morganp/openscad-festool-thincut/makerworld/cover_4x3.jpeg

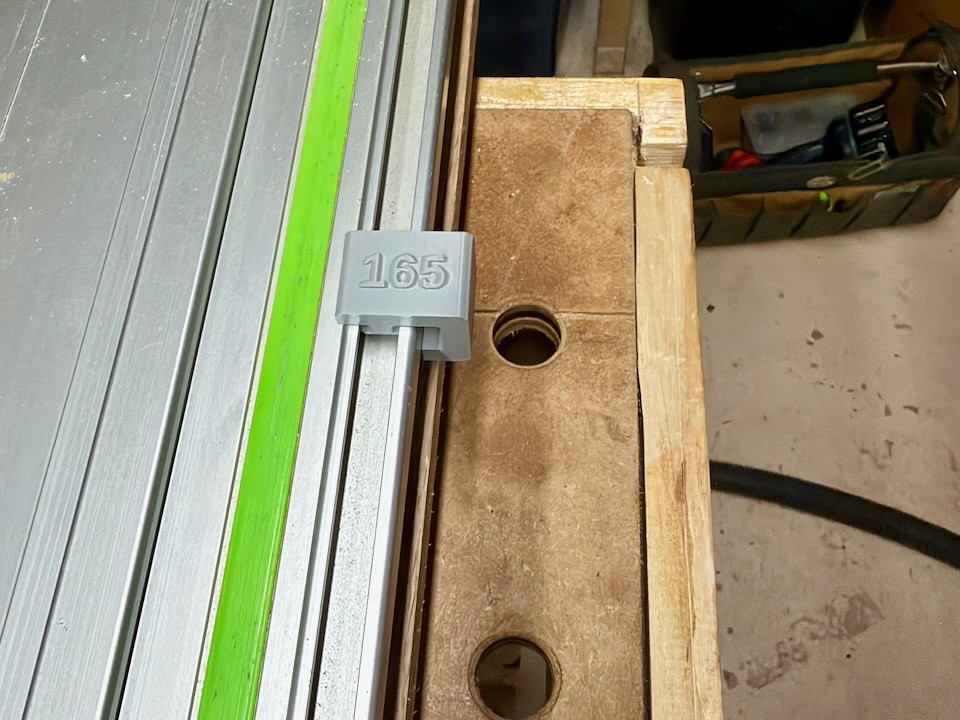
makerworld/cover_4x3.jpeg
