morganp/openscad-festool-thincut/makerworld/photo_2932.jpeg

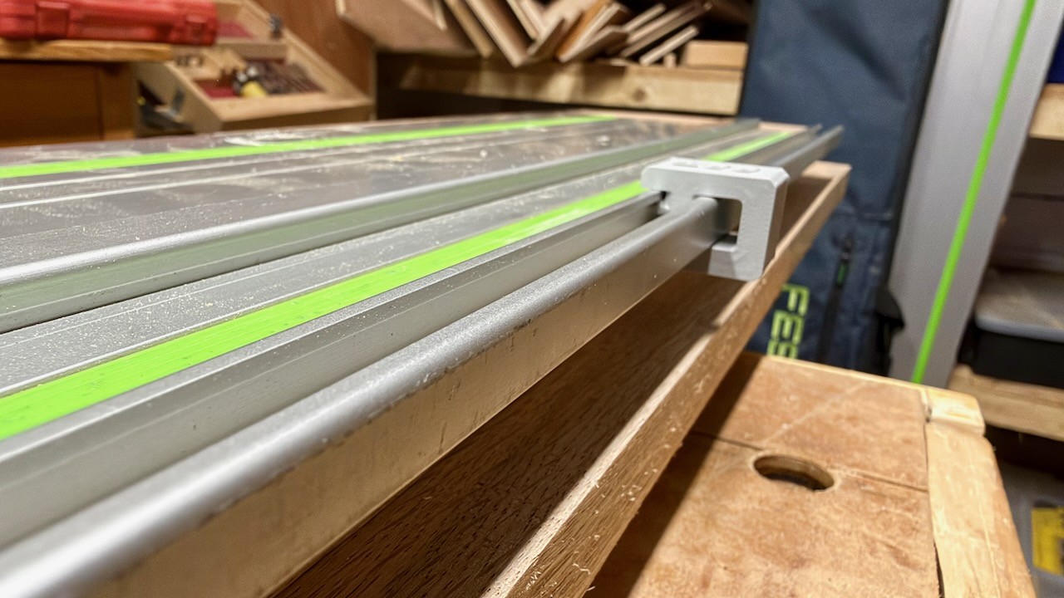
makerworld/photo_2932.jpeg
