morganp/openscad-festool-thincut/makerworld/photo_2934.jpeg

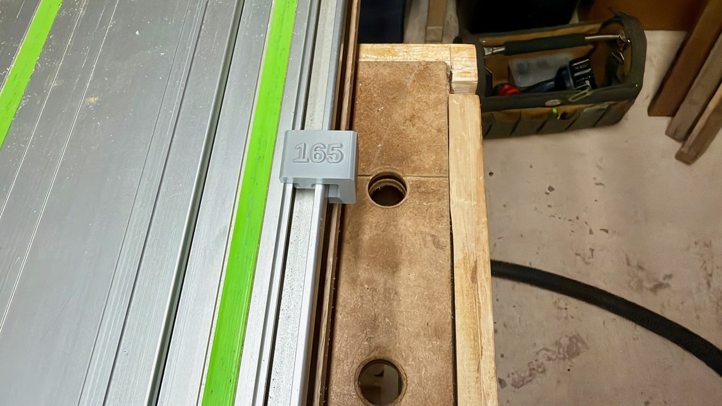
makerworld/photo_2934.jpeg
