morganp/openscad-festool-thincut/makerworld/photo_2935.jpeg

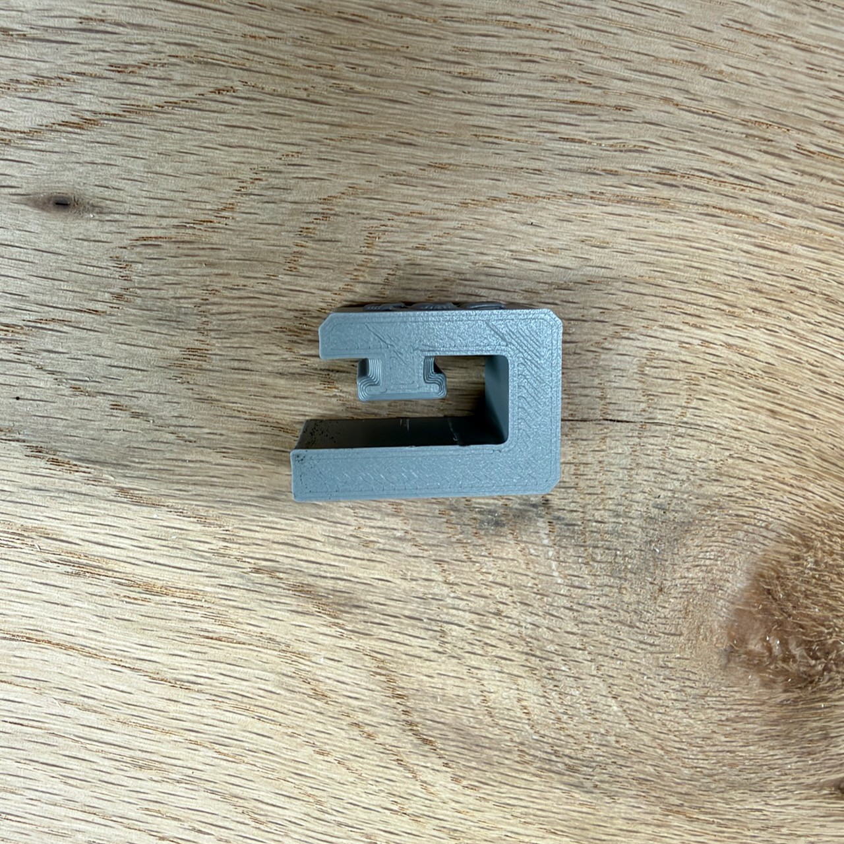
makerworld/photo_2935.jpeg
