morganp/openscad-festool-thincut/images/festool_thincut_key_test.png

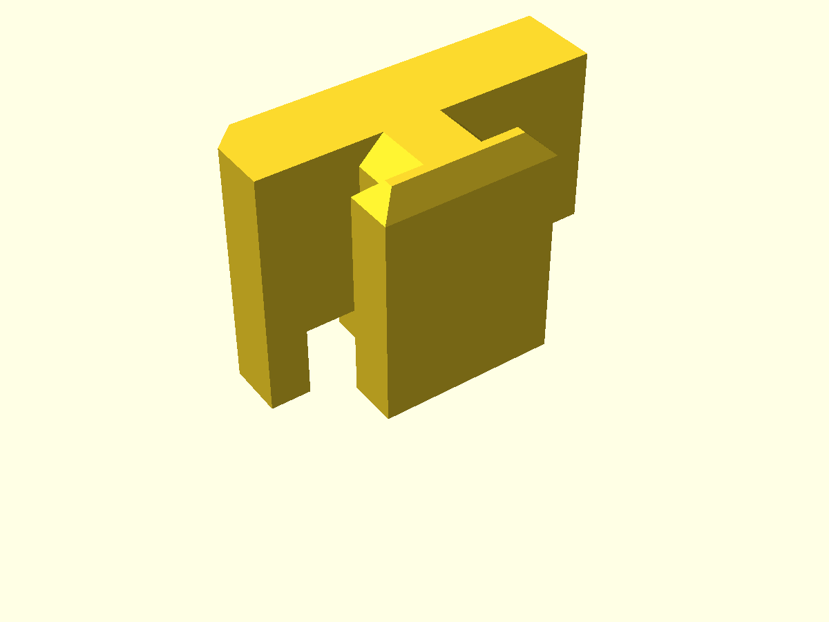
images/festool_thincut_key_test.png
